dkwasniak/zBox/cards_images/astronauta.png

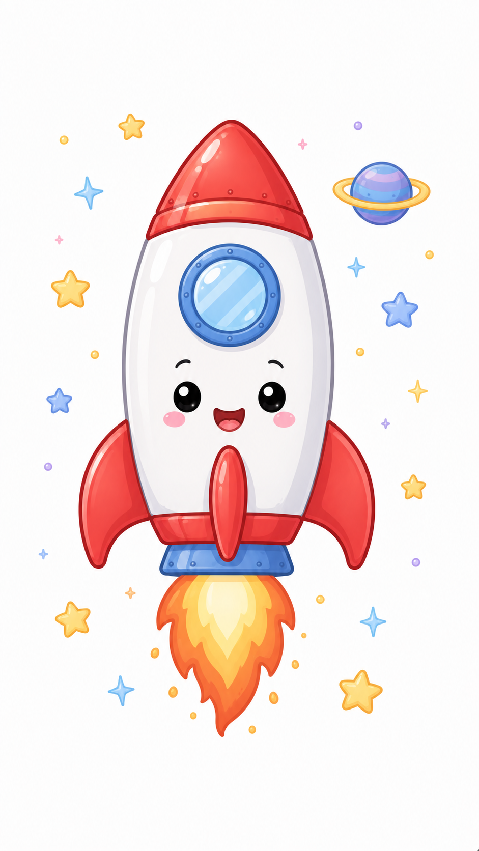
cards_images/astronauta.png
