dkwasniak/zBox/cards_images/balon.png

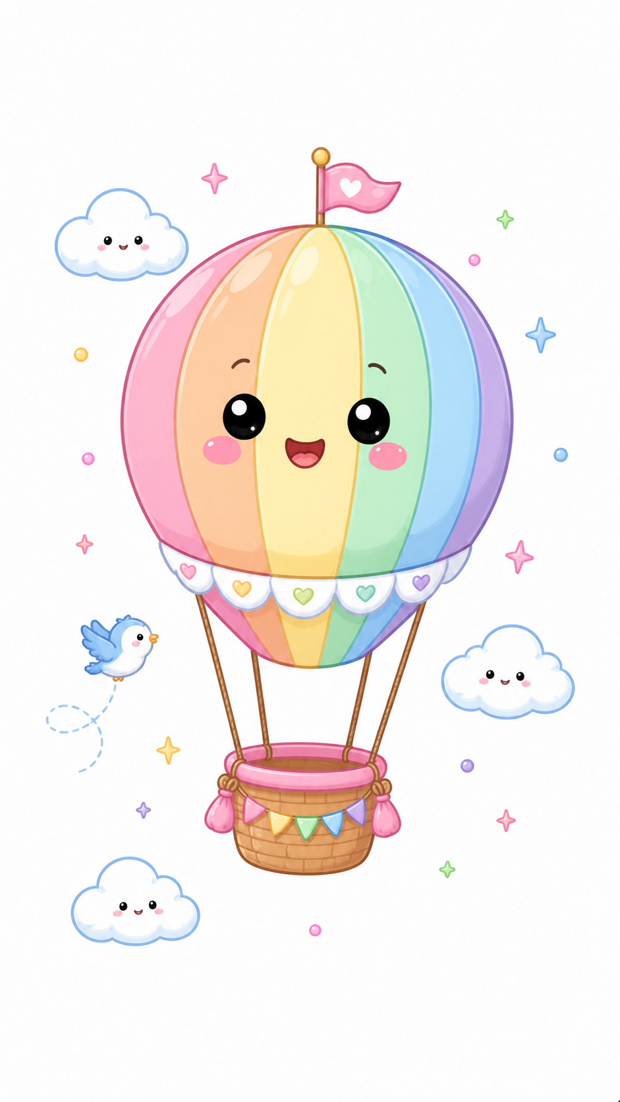
cards_images/balon.png
