dkwasniak/zBox/cards_images/balwan.png

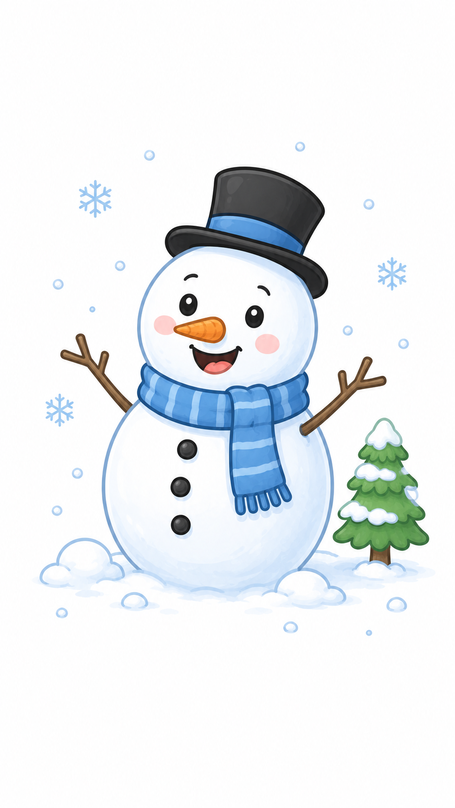
cards_images/balwan.png
