dkwasniak/zBox/cards_images/banan.png

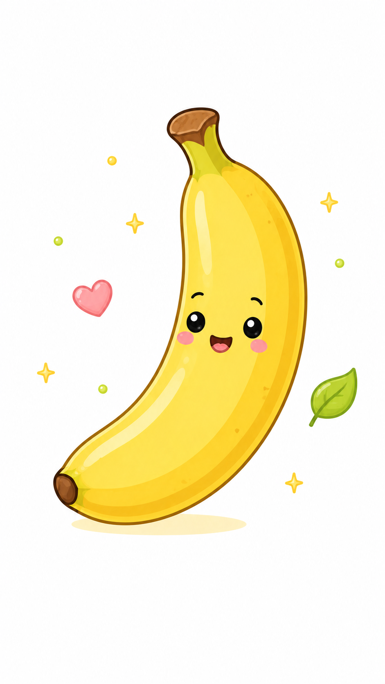
cards_images/banan.png
