dkwasniak/zBox/cards_images/beben.png

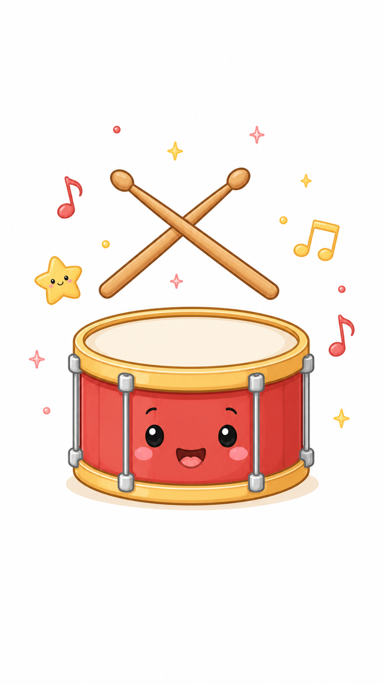
cards_images/beben.png
