dkwasniak/zBox/cards_images/domek.png

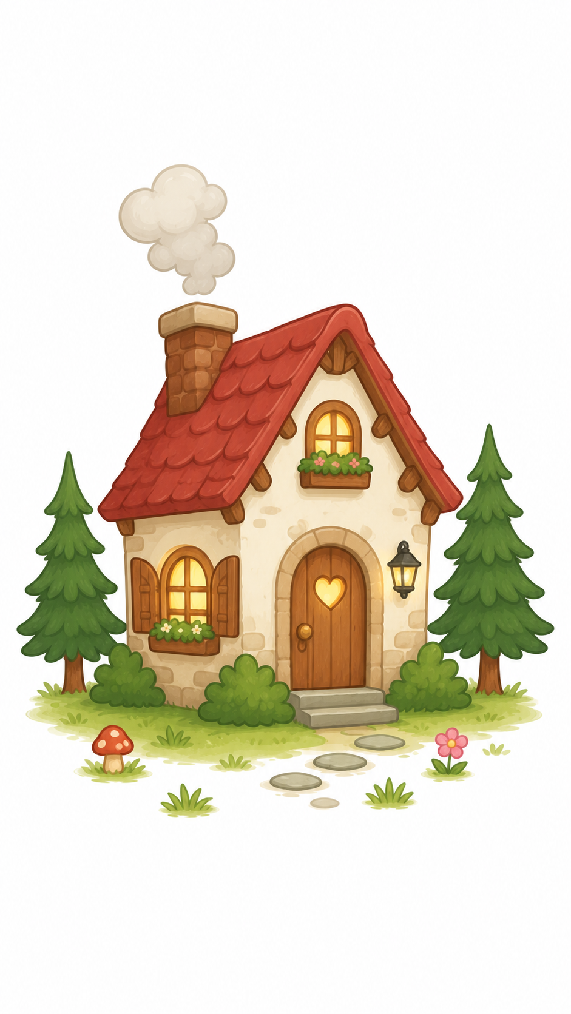
cards_images/domek.png
