dkwasniak/zBox/cards_images/drzewo.png

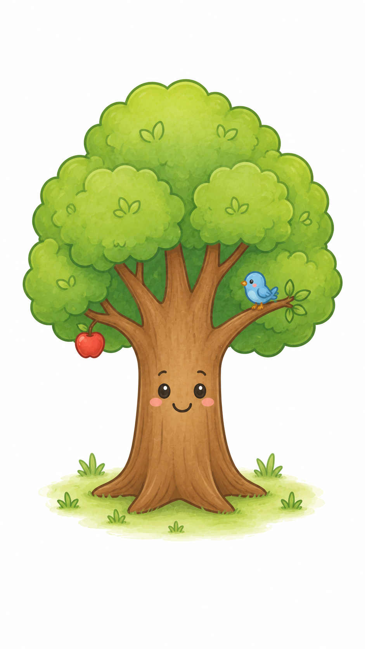
cards_images/drzewo.png
