dkwasniak/zBox/cards_images/gitara.png

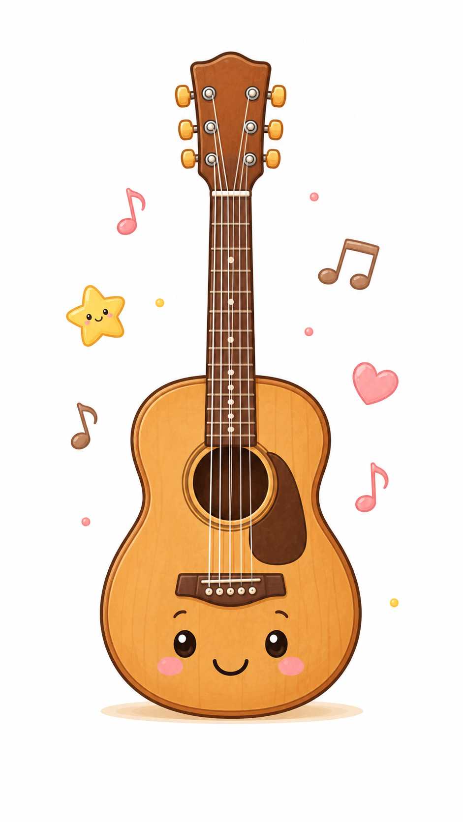
cards_images/gitara.png
