dkwasniak/zBox/cards_images/gwiazdka.png

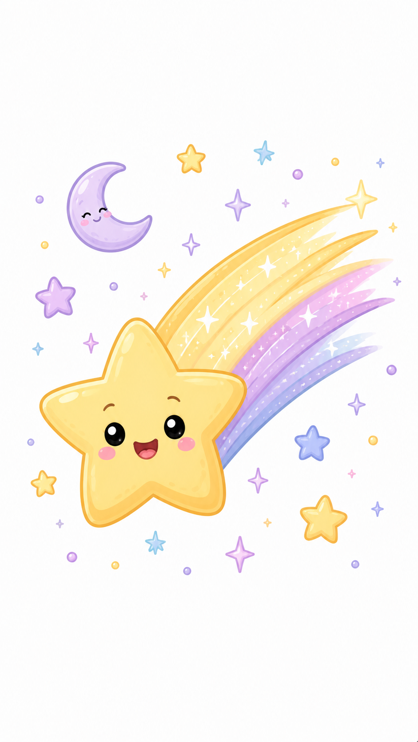
cards_images/gwiazdka.png
