dkwasniak/zBox/cards_images/helikopter.png

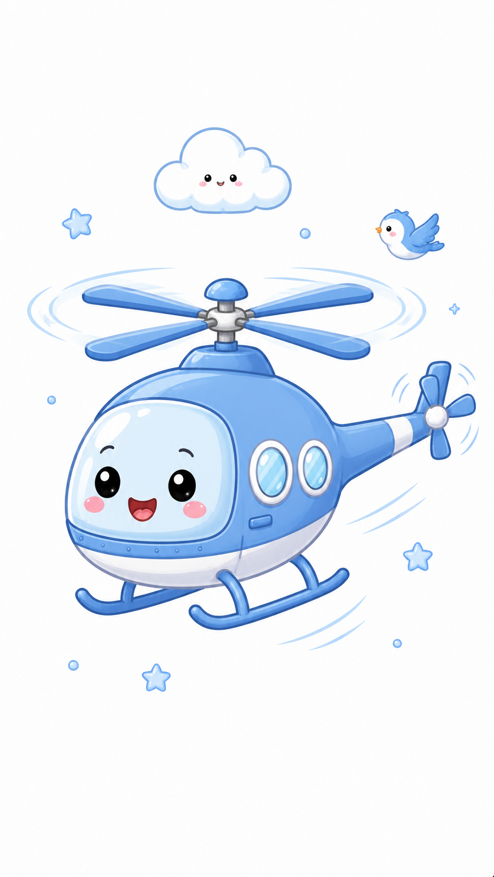
cards_images/helikopter.png
