dkwasniak/zBox/cards_images/jablko.png

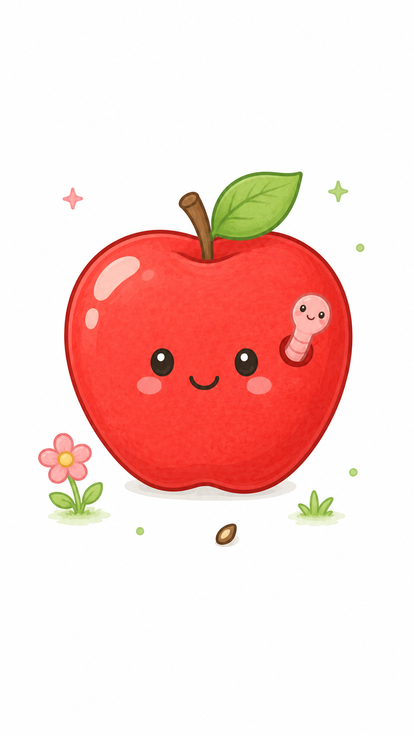
cards_images/jablko.png
