dkwasniak/zBox/cards_images/jednorozec.png

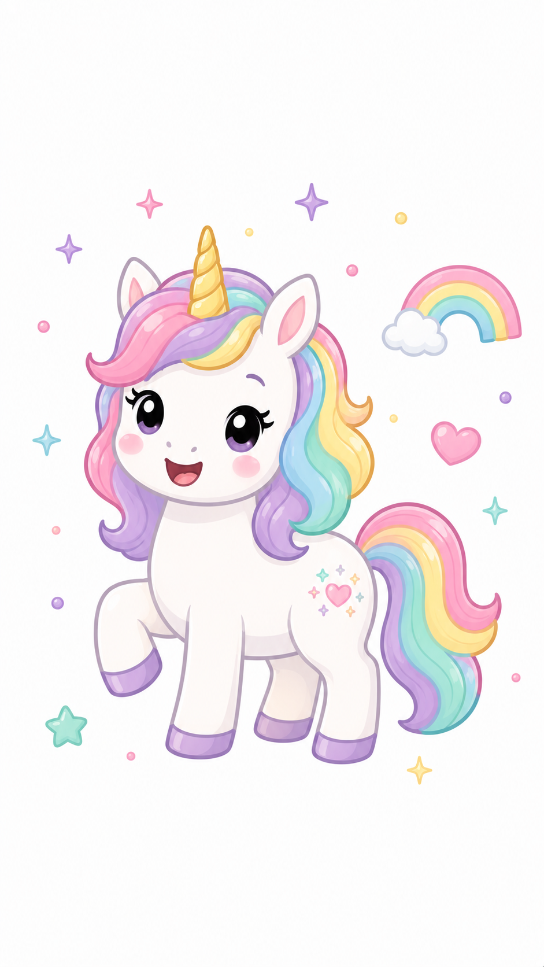
cards_images/jednorozec.png
