dkwasniak/zBox/cards_images/kometa.png

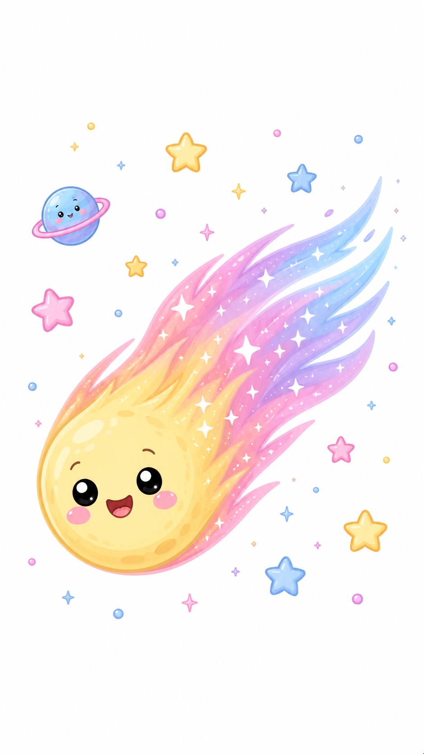
cards_images/kometa.png
