dkwasniak/zBox/cards_images/kot.png

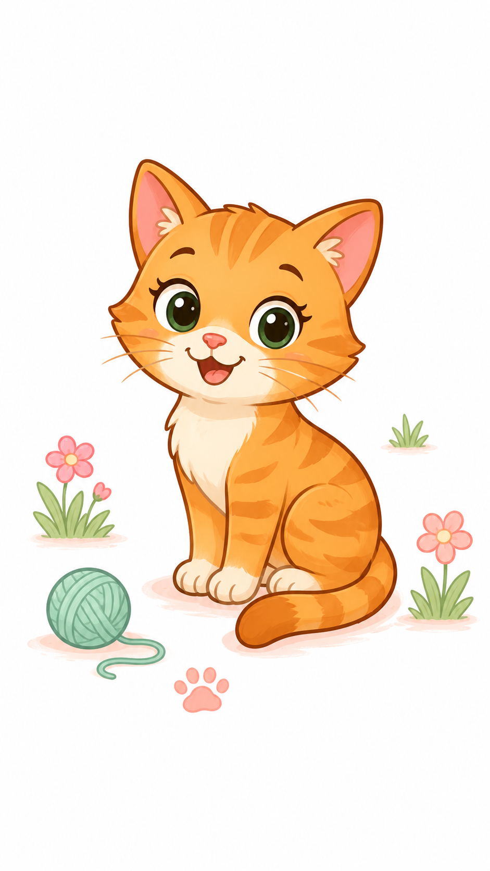
cards_images/kot.png
