dkwasniak/zBox/cards_images/krab.png

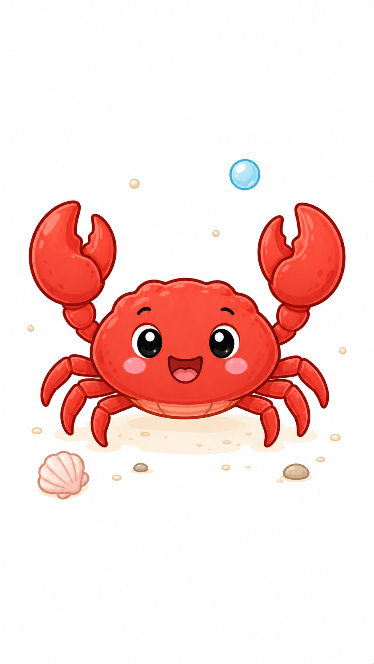
cards_images/krab.png
