dkwasniak/zBox/cards_images/krolik.png

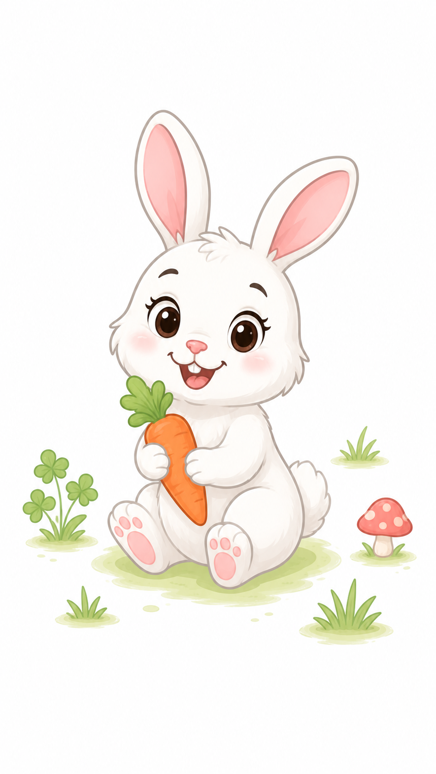
cards_images/krolik.png
