dkwasniak/zBox/cards_images/krowa.png

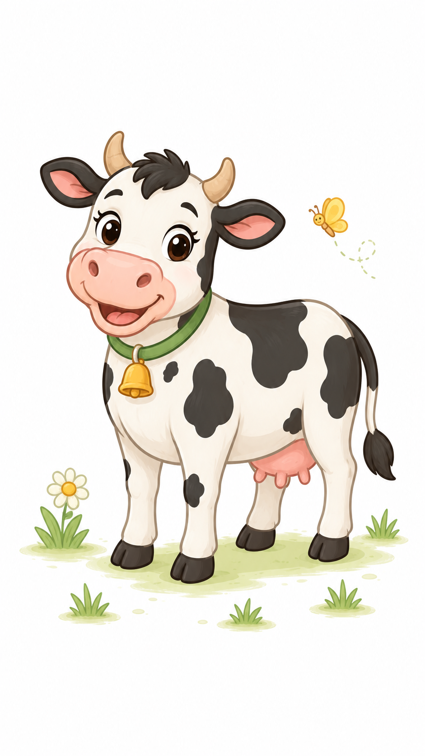
cards_images/krowa.png
