dkwasniak/zBox/cards_images/kwiat.png

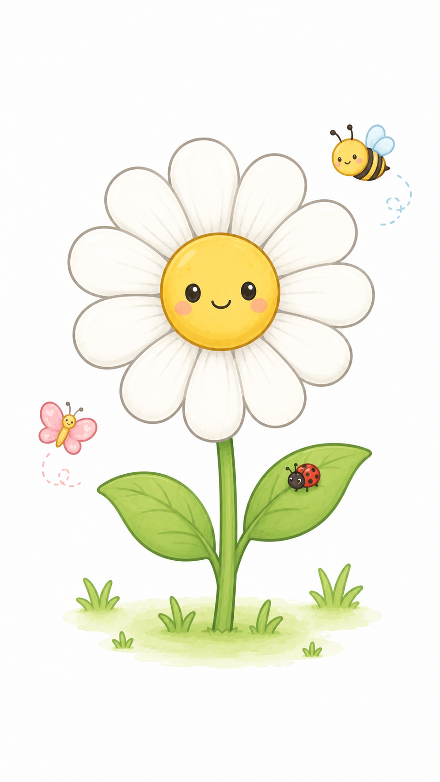
cards_images/kwiat.png
