dkwasniak/zBox/cards_images/lew.png

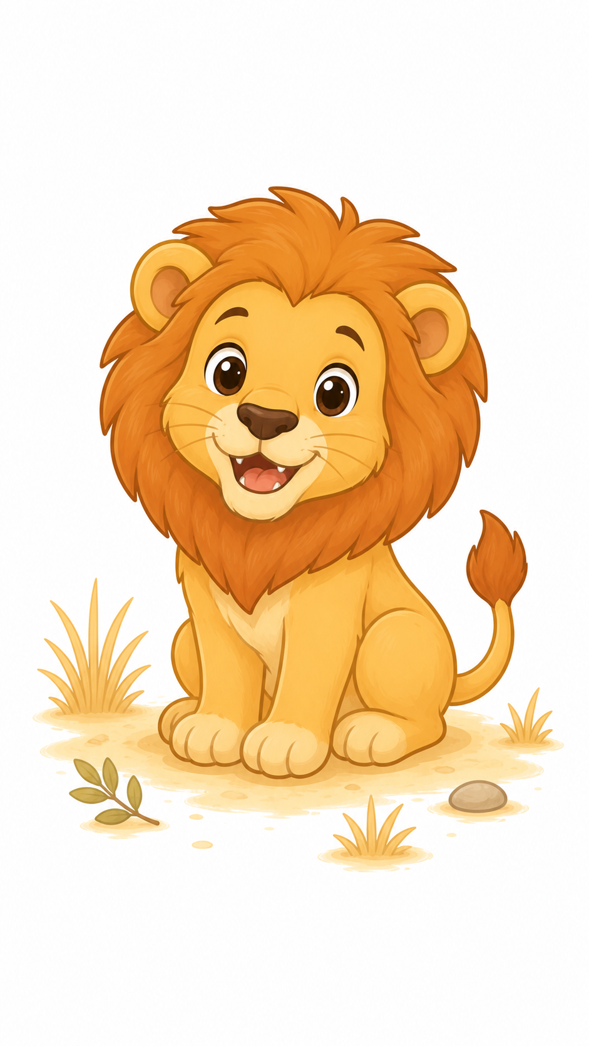
cards_images/lew.png
