dkwasniak/zBox/cards_images/lodka1.png

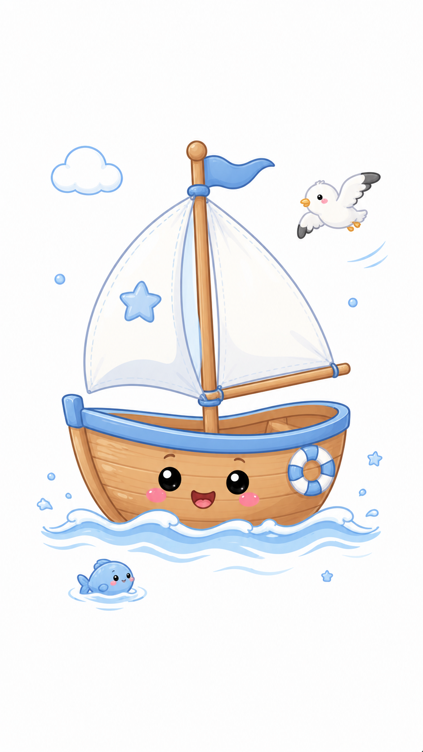
cards_images/lodka1.png
