dkwasniak/zBox/cards_images/malpa.png

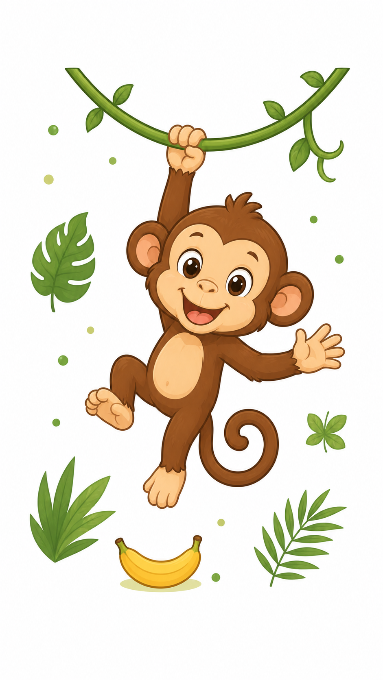
cards_images/malpa.png
