dkwasniak/zBox/cards_images/marchewka.png

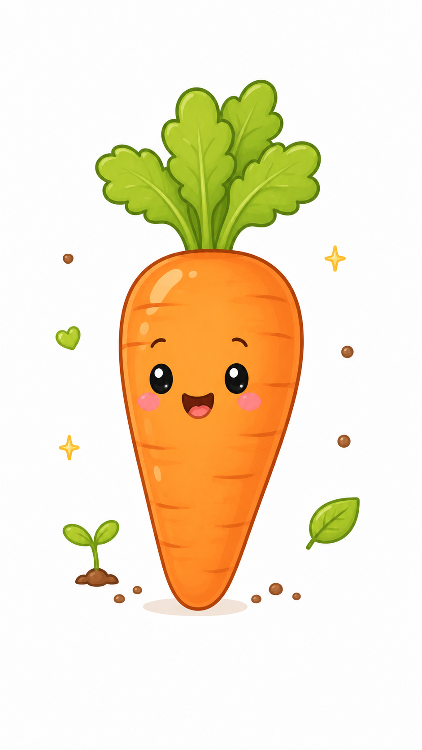
cards_images/marchewka.png
