dkwasniak/zBox/cards_images/niedzwiedz.png

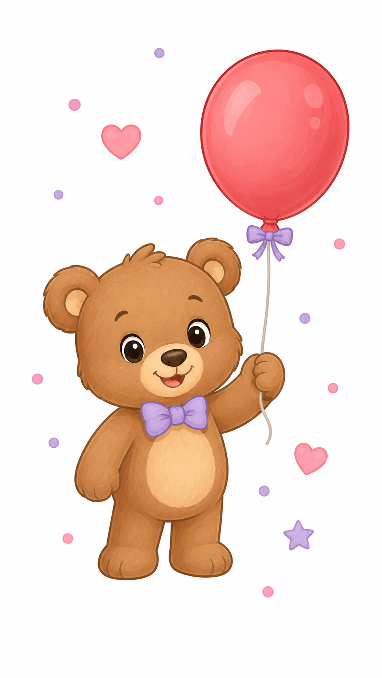
cards_images/niedzwiedz.png
