dkwasniak/zBox/cards_images/panda.png

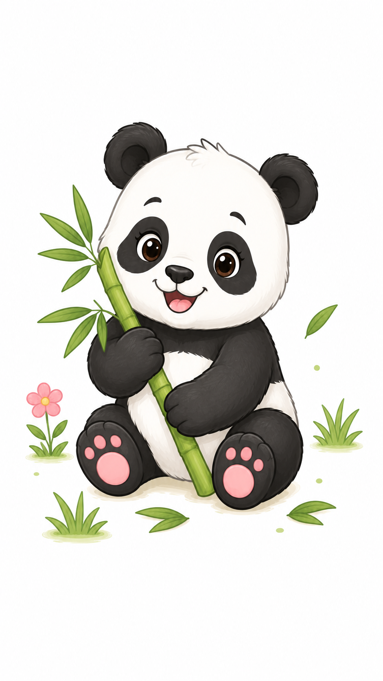
cards_images/panda.png
