dkwasniak/zBox/cards_images/planeta.png

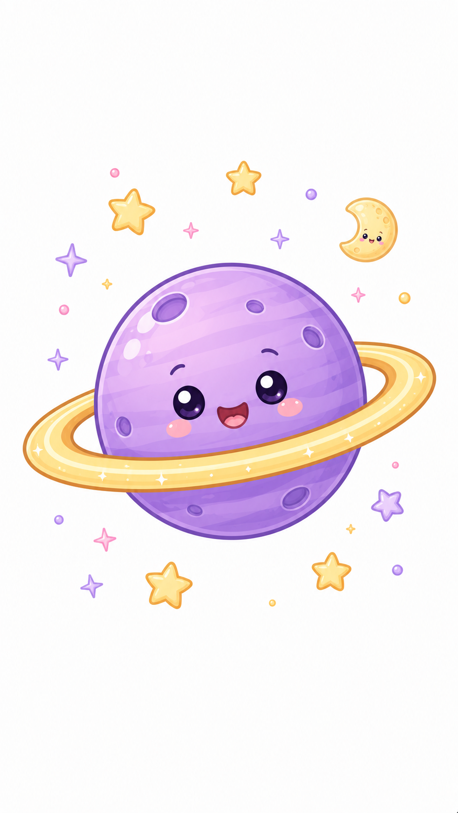
cards_images/planeta.png
