dkwasniak/zBox/cards_images/pociag.png

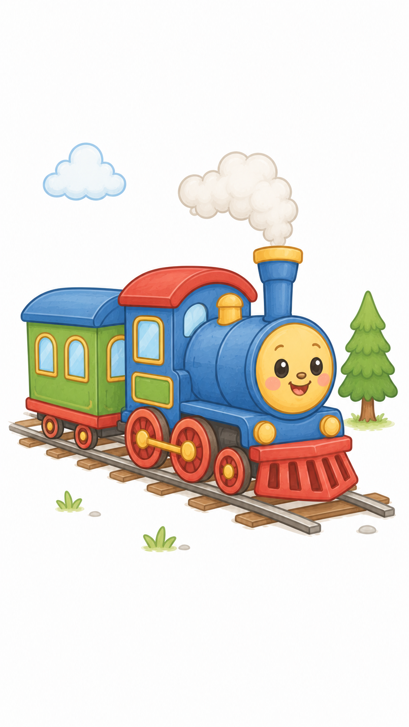
cards_images/pociag.png
