dkwasniak/zBox/cards_images/rybka.png

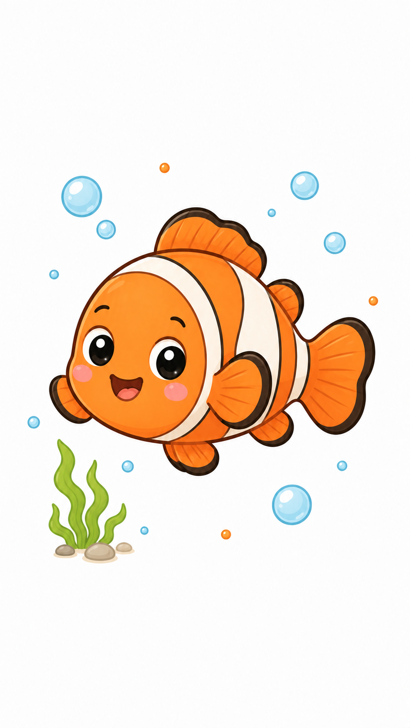
cards_images/rybka.png
