dkwasniak/zBox/cards_images/samochod.png

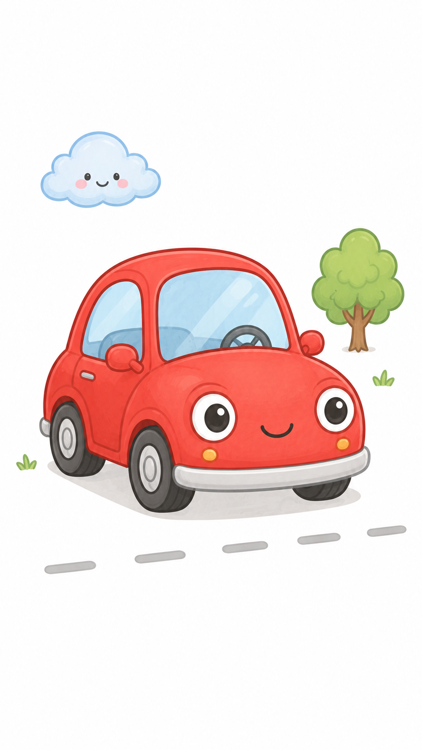
cards_images/samochod.png
