dkwasniak/zBox/cards_images/samolot1.png

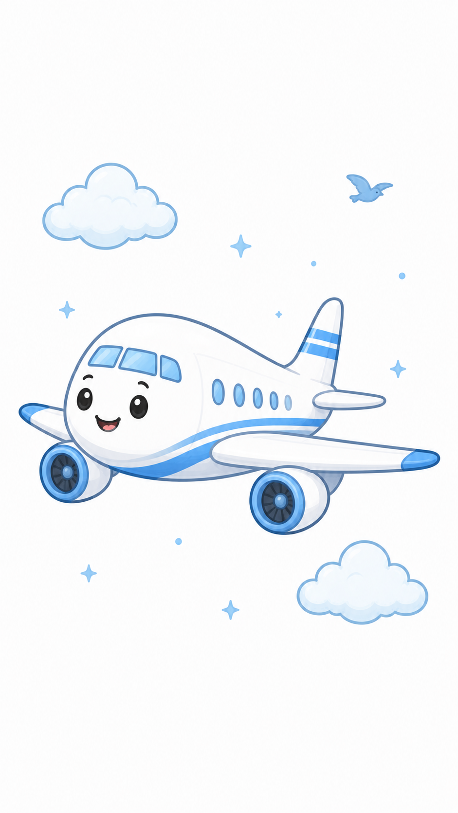
cards_images/samolot1.png
