dkwasniak/zBox/cards_images/slon.png

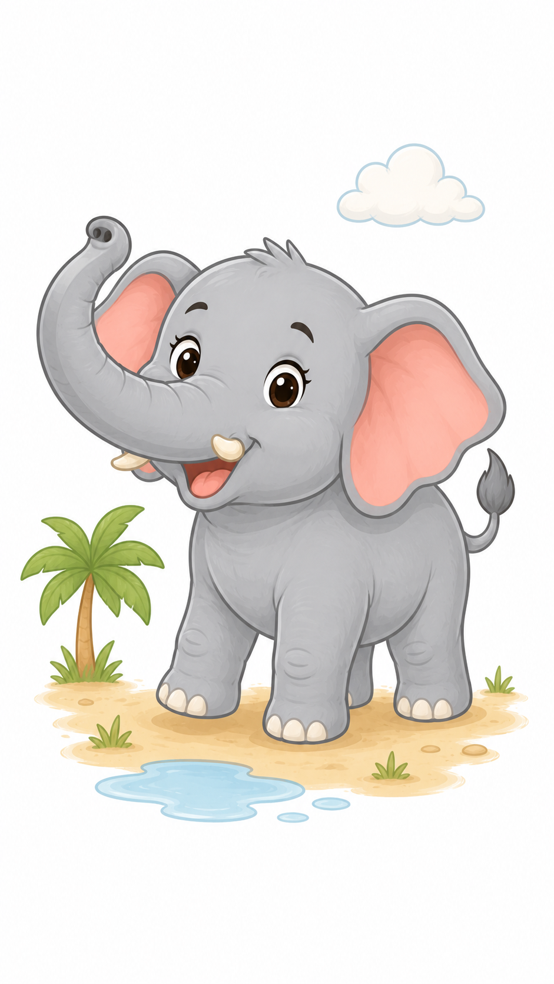
cards_images/slon.png
