dkwasniak/zBox/cards_images/slonce.png

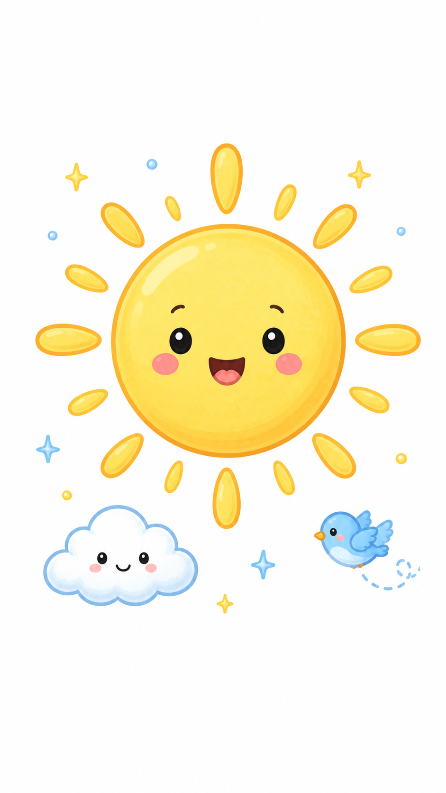
cards_images/slonce.png
