dkwasniak/zBox/cards_images/smok.png

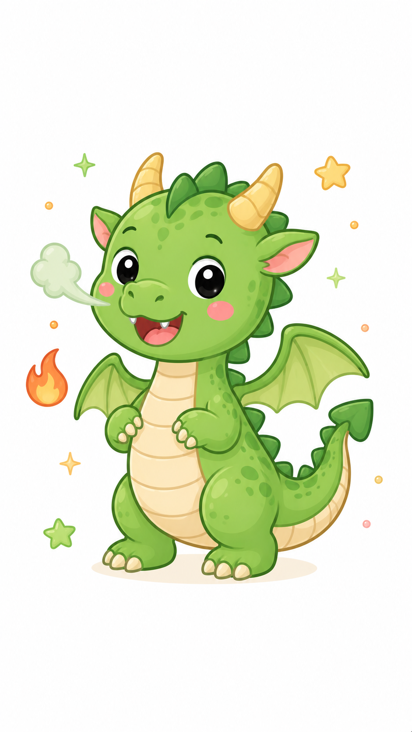
cards_images/smok.png
