dkwasniak/zBox/cards_images/tecza.png

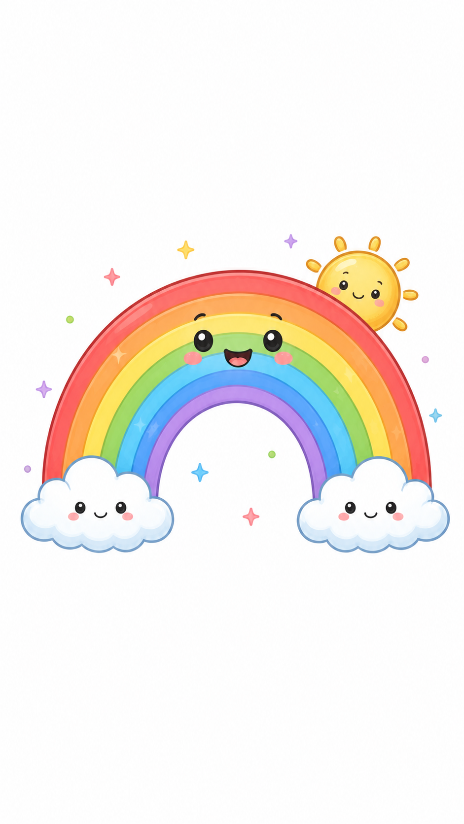
cards_images/tecza.png
