dkwasniak/zBox/cards_images/tosty.png

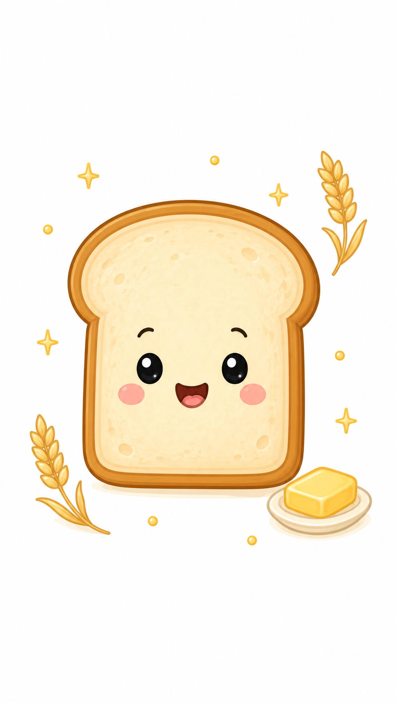
cards_images/tosty.png
