dkwasniak/zBox/cards_images/zamek.png

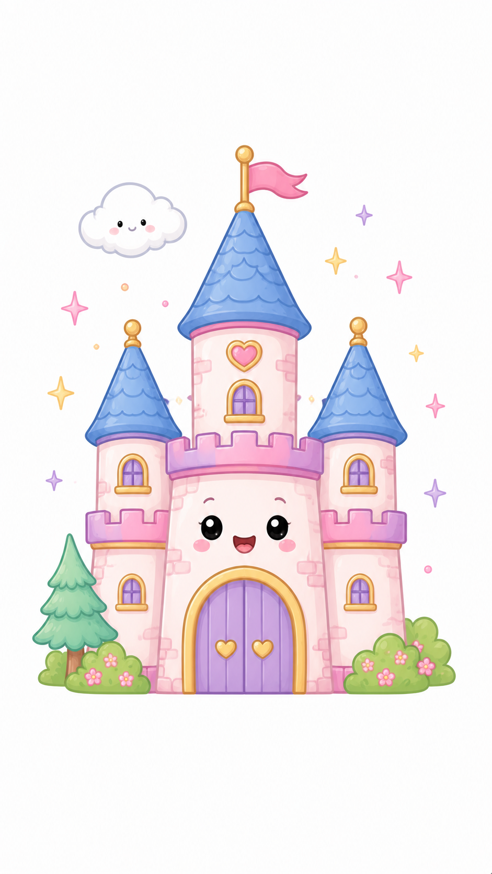
cards_images/zamek.png
